xyphro/UsbGpib/HW/REV2/Layout.png

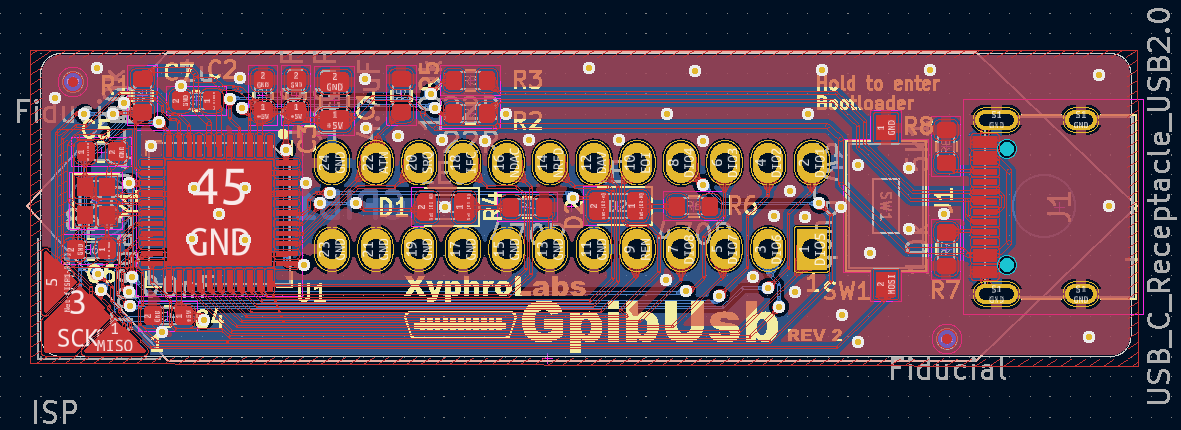
HW/REV2/Layout.png
