xyphro/UsbGpib/pictures/cleaning.jpg

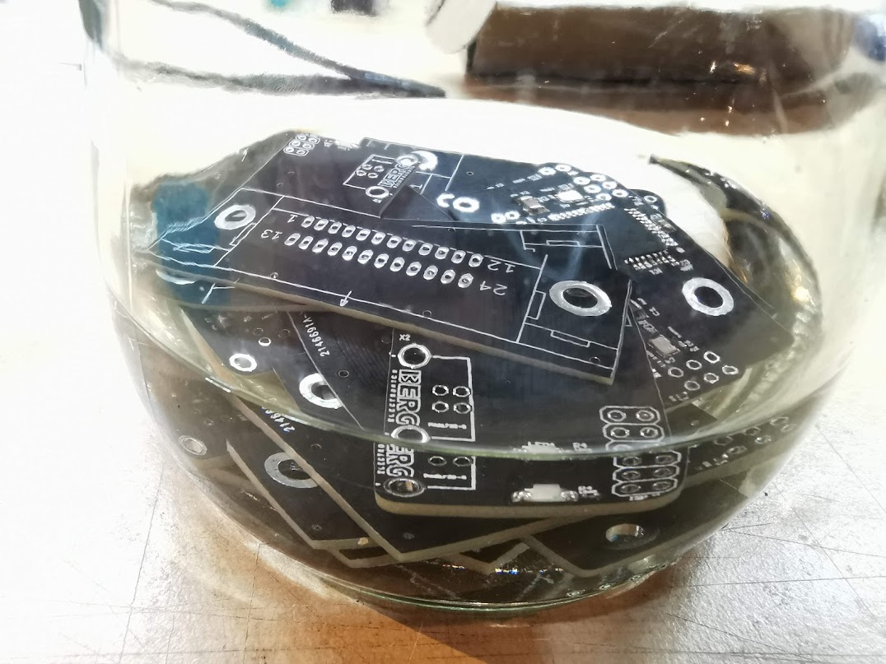
pictures/cleaning.jpg
