xyphro/UsbGpib/pictures/finalmounting.jpg

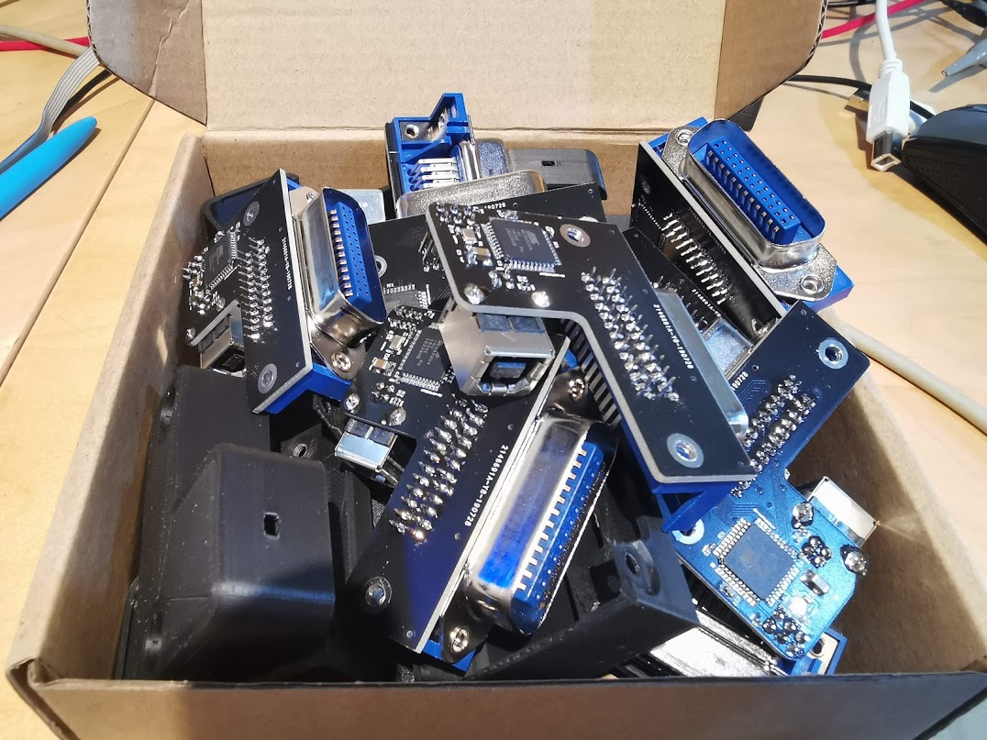
pictures/finalmounting.jpg
