xyphro/UsbGpib/pictures/mounting.jpg

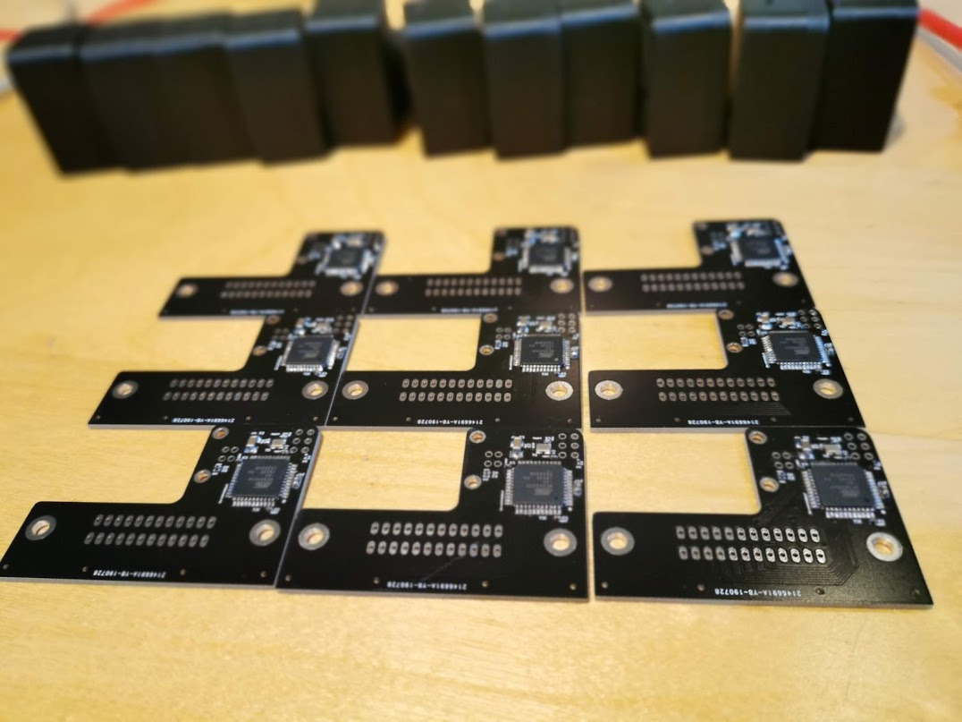
pictures/mounting.jpg
