xyphro/UsbGpib/pictures/outlook_Rev2.jpg

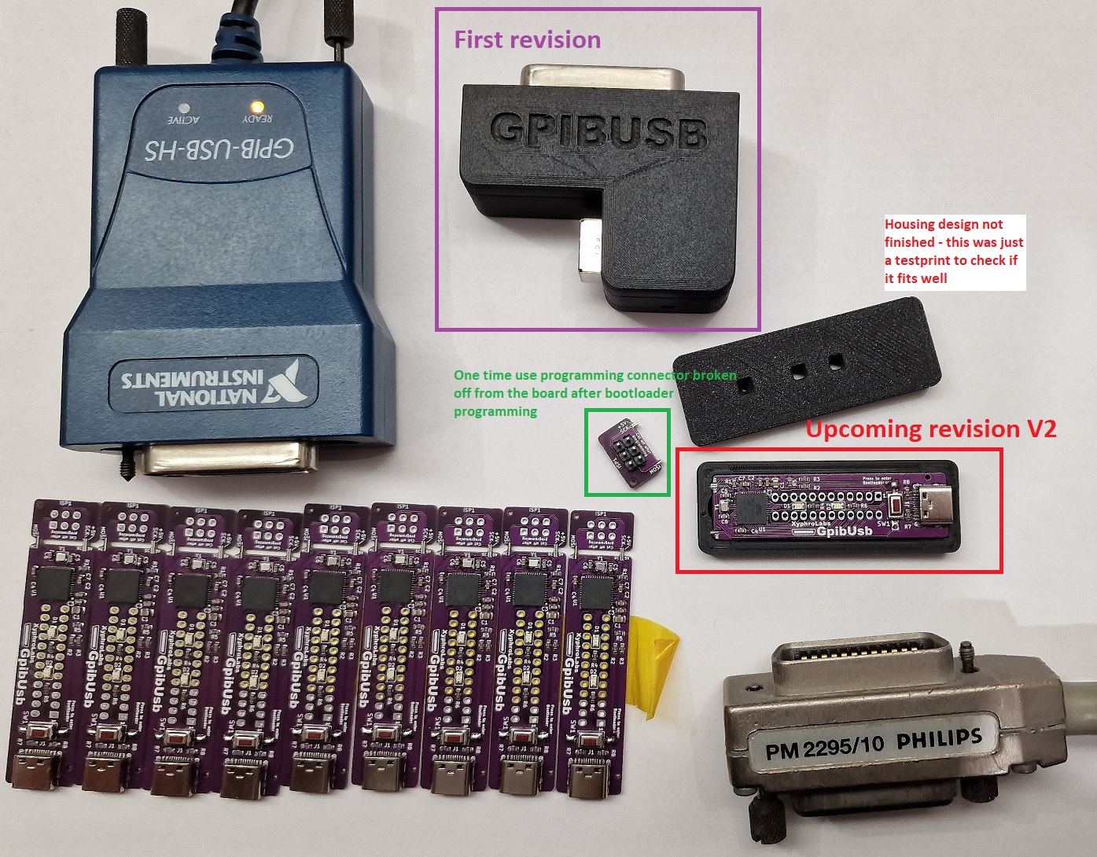
pictures/outlook_Rev2.jpg
