xyphro/UsbGpib/pictures/UpcomingHWRevision.png

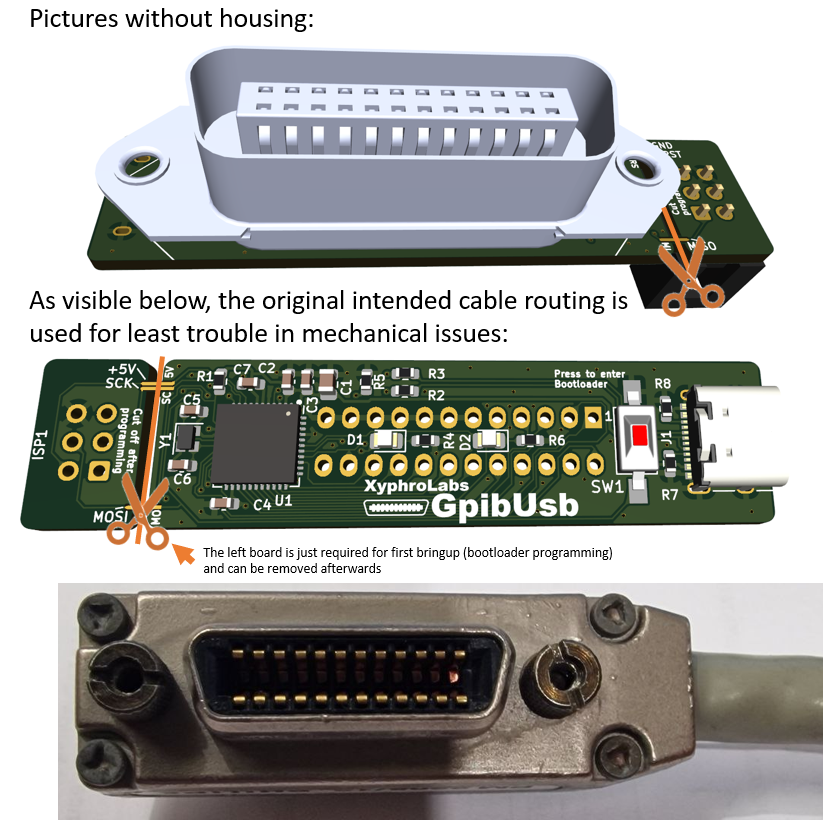
pictures/UpcomingHWRevision.png
