xyphro/UsbGpib/pictures/UsbGpibV2.jpg

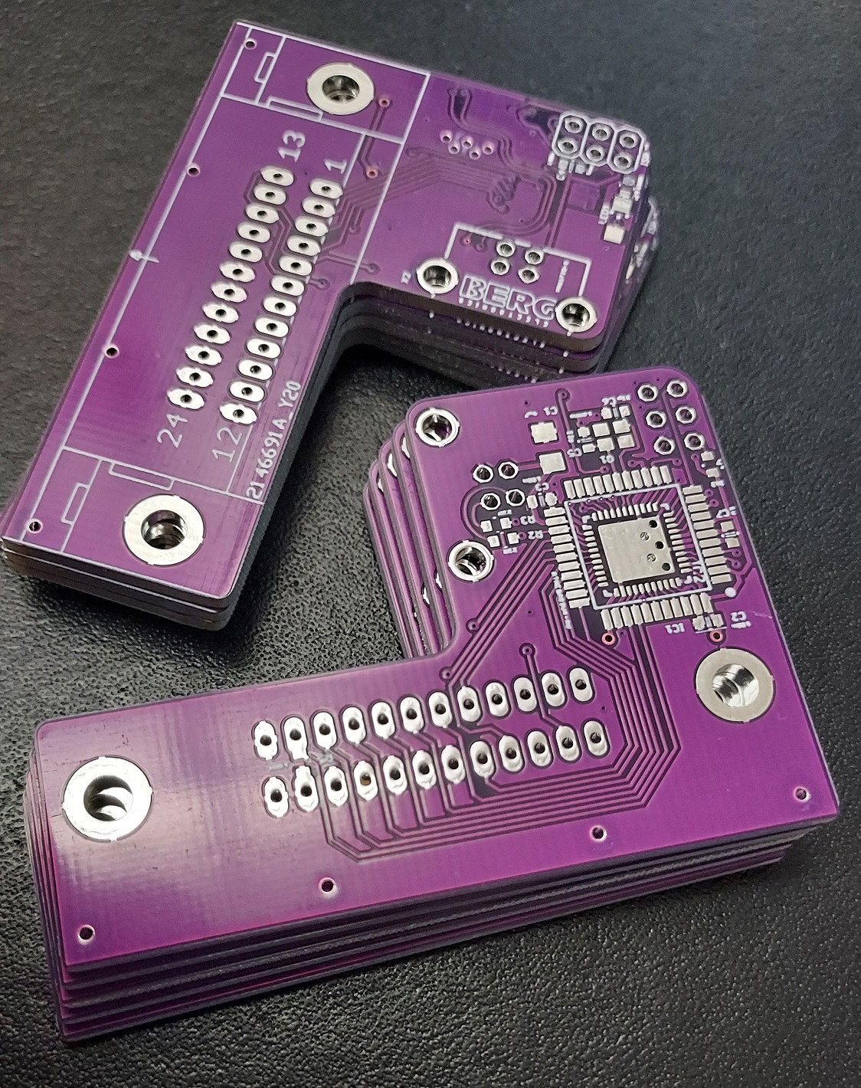
pictures/UsbGpibV2.jpg
