xyphro/UsbGpib/SW/TestAndMeasurement/TestAndMeasurement.h

/*
             LUFA Library
     Copyright (C) Dean Camera, 2019.

  dean [at] fourwalledcubicle [dot] com
           www.lufa-lib.org
*/

/*
  Copyright 2019  Dean Camera (dean [at] fourwalledcubicle [dot] com)

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
  The author disclaims all warranties with regard to this
  software, including all implied warranties of merchantability
  and fitness.  In no event shall the author be liable for any
  special, indirect or consequential damages or any damages
  whatsoever resulting from loss of use, data or profits, whether
  in an action of contract, negligence or other tortious action,
  arising out of or in connection with the use or performance of
  this software.
*/

#ifndef _TESTANDMEASUREMENT_H_
#define _TESTANDMEASUREMENT_H_

	/* Includes: */
		#include <avr/io.h>
		#include <avr/wdt.h>
		#include <avr/power.h>
		#include <avr/interrupt.h>

		#include "Descriptors.h"

		#include <LUFA/Drivers/Board/LEDs.h>
		#include <LUFA/Drivers/USB/USB.h>
		#include <LUFA/Platform/Platform.h>

	/* Macros: */
		/** LED mask for the library LED driver, to indicate that the USB interface is not ready. */
		#define LEDMASK_USB_NOTREADY                  LEDS_LED1

		/** LED mask for the library LED driver, to indicate that the USB interface is enumerating. */
		#define LEDMASK_USB_ENUMERATING              (LEDS_LED2 | LEDS_LED3)

		/** LED mask for the library LED driver, to indicate that the USB interface is ready. */
		#define LEDMASK_USB_READY                    (LEDS_LED2 | LEDS_LED4)

		/** LED mask for the library LED driver, to indicate that an error has occurred in the USB interface. */
		#define LEDMASK_USB_ERROR                    (LEDS_LED1 | LEDS_LED3)

		/** LED mask for the library LED driver, to indicate that the USB interface is busy. */
		#define LEDMASK_USB_BUSY                      LEDS_LED2

		#define Req_InitiateAbortBulkOut              0x01
		#define Req_CheckAbortBulkOutStatus           0x02
		#define Req_InitiateAbortBulkIn               0x03
		#define Req_CheckAbortBulkInStatus            0x04
		#define Req_InitiateClear                     0x05
		#define Req_CheckClearStatus                  0x06
		#define Req_GetCapabilities                   0x07
		#define Req_IndicatorPulse                    0x40
		#define Req_ReadStatusByte                    0x80
		#define Req_RenControl 						  160
		#define Req_GoToLocal						  161
		#define Req_LocalLockout                      162

		#define TMC_STATUS_SUCCESS                    0x01
		#define TMC_STATUS_PENDING                    0x02
		#define TMC_STATUS_INTERRUPT_IN_BUSY		  0x20

		#define TMC_STATUS_FAILED                     0x80
		#define TMC_STATUS_TRANSFER_NOT_IN_PROGRESS   0x81
		#define TMC_STATUS_SPLIT_NOT_IN_PROGRESS      0x82
		#define TMC_STATUS_SPLIT_IN_PROGRESS          0x83

		#define TMC_MESSAGEID_DEV_DEP_MSG_OUT         0x01
		#define TMC_MESSAGEID_DEV_DEP_MSG_IN          0x02
		#define TMC_MESSAGEID_DEV_VENDOR_OUT          0x7E
		#define TMC_MESSAGEID_DEV_VENDOR_IN           0x7F
		#define TMC_MESSAGEID_TRIGGER                 0x80
		

	/* Type Defines */
		typedef struct
		{
			uint8_t  Status;
			uint8_t  Reserved;

			uint16_t TMCVersion;

			struct
			{
				unsigned ListenOnly             : 1; /* Bit 0 */
				unsigned TalkOnly               : 1;
				unsigned PulseIndicateSupported : 1;
				unsigned Reserved               : 5;
			} Interface;

			struct
			{
				unsigned SupportsAbortINOnMatch : 1;
				unsigned Reserved               : 7;
			} Device;
// offset 7:
			uint8_t Reserved2[6];
// Here subclass 488 extended capabilities:	
			uint16_t bcdUSB488; /*0x0100 or greater */
			struct {
				unsigned SupportTrigger         : 1; /* 1 if trigger is supported */
				unsigned SupportRenControl      : 1; /* 1 if remote enable control is supported */
				unsigned Is488IF                : 1; /* 1 if this is a 488.2 interface (488.1 if 0)*/
				unsigned Reserved               : 5;				
			} USB488IfCap1;
			struct {
				unsigned DT1Capable             : 1; /* 1 if DT1 capable, otherwise 0 for DT0 */
				unsigned RL1Capable             : 1; /* 1 if RL1 capable, otherwise 0 for RL0  */
				unsigned SR1Capable             : 1; /* 1 if SR1 capable, otherwise 0 for SR0  */
				unsigned MandatorySCPI          : 1; /* 1 if all 488.2 mandatory SCPI commands are supported */
				unsigned Reserved               : 4;
			} USB488IfCap2;
			uint8_t Reserved3[8];
		} TMC_Capabilities_t;

		typedef struct
		{
			uint8_t LastMessageTransaction;
			uint8_t TermChar;
			uint8_t Reserved[2];
		} TMC_DevOUTMessageHeader_t;

		typedef struct
		{
			uint8_t LastMessageTransaction;
			uint8_t TermChar;
			uint8_t Reserved[2];
		} TMC_DevINMessageHeader_t;

		typedef struct
		{
			uint8_t  MessageID;
			uint8_t  Tag;
			uint8_t  InverseTag;
			uint8_t  Reserved;
			uint32_t TransferSize;

			union
			{
				TMC_DevOUTMessageHeader_t DeviceOUT;
				TMC_DevINMessageHeader_t  DeviceIN;
				uint32_t                  VendorSpecific;
			} MessageIDSpecific;
		} TMC_MessageHeader_t;

	/* Function Prototypes: */
		void SetupHardware(void);
		//void TMC_Task(void);
		bool ReadTMCHeader(TMC_MessageHeader_t* const MessageHeader);
		bool WriteTMCHeader(TMC_MessageHeader_t* const MessageHeader);

		void EVENT_USB_Device_Connect(void);
		void EVENT_USB_Device_Disconnect(void);
		void EVENT_USB_Device_ConfigurationChanged(void);
		void EVENT_USB_Device_ControlRequest(void);
		
		void eeprom_update_if_changed(uint16_t addr, uint8_t value);
		
		void set_internal_response(uint8_t *pdat, uint8_t len);
		
		void Jump_To_Bootloader(void);

#endif
